andywestthorp/Machine_Safety_System_Facial_Recognition_Addon/arduino/DT-Safety_System/images.h

// 'green_tick_circle', 23x22px
const unsigned char  green_tick_circle [] PROGMEM = {
  0xff, 0xff, 0xfe, 0xff, 0xe7, 0xfe, 0xfe, 0x00, 0x7e, 0xfc, 0x00, 0x3e, 0xf8, 0x00, 0x1e, 0xf0,
  0x00, 0x4e, 0xe0, 0x00, 0xe6, 0xe0, 0x01, 0xe6, 0xe0, 0x03, 0xc6, 0xe2, 0x07, 0x86, 0xc7, 0x0f,
  0x02, 0xc7, 0x9e, 0x02, 0xe3, 0xfc, 0x06, 0xe1, 0xf8, 0x06, 0xe0, 0xf0, 0x06, 0xe0, 0x60, 0x06,
  0xf0, 0x00, 0x0e, 0xf8, 0x00, 0x1e, 0xfc, 0x00, 0x3e, 0xfe, 0x00, 0x7e, 0xff, 0xe7, 0xfe, 0xff,
  0xff, 0xfe
};
// 'spanner', 100x107px
const unsigned char  spanner [] PROGMEM = {
  0xff, 0xff, 0xff, 0xff, 0xff, 0xff, 0xff, 0xff, 0xff, 0xff, 0xff, 0xff, 0xf0, 0xff, 0xff, 0xff,
  0xff, 0xff, 0xff, 0xff, 0xff, 0xff, 0xff, 0xff, 0xff, 0xf0, 0xff, 0xff, 0xff, 0xff, 0xff, 0xff,
  0xff, 0xff, 0xff, 0xff, 0xff, 0xff, 0xf0, 0xff, 0xff, 0xff, 0xff, 0xff, 0xff, 0xff, 0xff, 0xfe,
  0x03, 0xff, 0xff, 0xf0, 0xff, 0xff, 0xff, 0xff, 0xff, 0xff, 0xff, 0xff, 0xf1, 0xff, 0x3f, 0xff,
  0xf0, 0xff, 0xff, 0xff, 0xff, 0xff, 0xff, 0xff, 0xff, 0x98, 0x00, 0x7f, 0xff, 0xf0, 0xff, 0xff,
  0xff, 0xff, 0xff, 0xff, 0xff, 0xfe, 0xe0, 0x00, 0xbf, 0xff, 0xf0, 0xff, 0xff, 0xff, 0xff, 0xff,
  0xff, 0xff, 0xfd, 0x00, 0x01, 0x7f, 0xff, 0xf0, 0xff, 0xff, 0xff, 0xff, 0xff, 0xff, 0xff, 0xfa,
  0x00, 0x02, 0xff, 0xff, 0xf0, 0xff, 0xff, 0xff, 0xff, 0xff, 0xff, 0xff, 0xe4, 0x00, 0x05, 0xff,
  0xff, 0xf0, 0xff, 0xff, 0xff, 0xff, 0xff, 0xff, 0xff, 0xe8, 0x00, 0x0b, 0xff, 0xff, 0xf0, 0xff,
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
const int  allArray_LEN = 15;
const unsigned char*  allArray[15] = {
  Scan,
  eyeprot,
  green_tick_circle,
  logo,
  network_fault,
  network_ok,
  networkok,
  rfid_fault,
  rfid_ok2,
  spanner,
  vacuum,
  wifi_fault,
  wifi_ok,
  write_rfid
};
